yuburoll/ANSIC/images/ansicBackplates.jpg

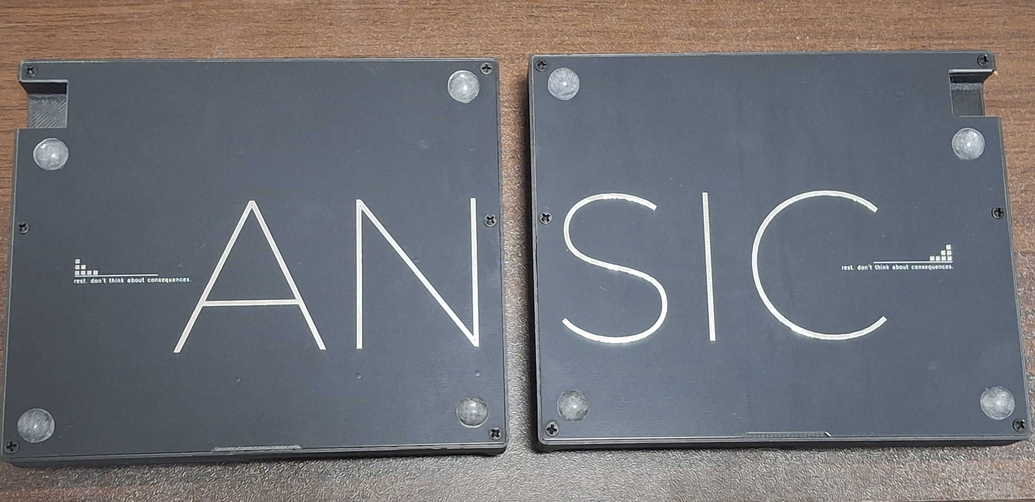
images/ansicBackplates.jpg
