yuburoll/ANSIC/images/ansicChipset1.jpg

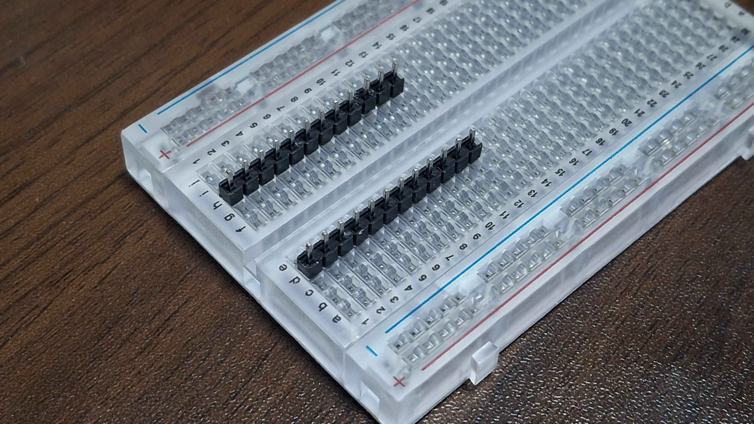
images/ansicChipset1.jpg
