yuburoll/ANSIC/images/ansicChipset2.jpg

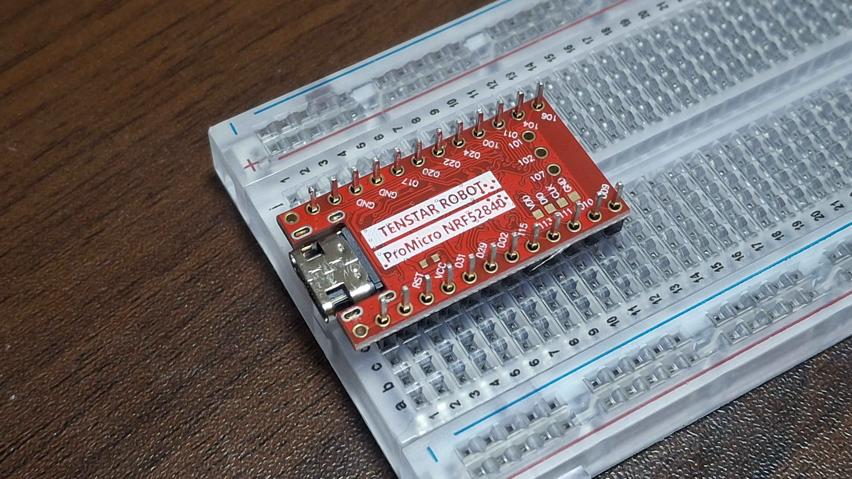
images/ansicChipset2.jpg
