yuburoll/ANSIC/images/ansicChipset3.jpg

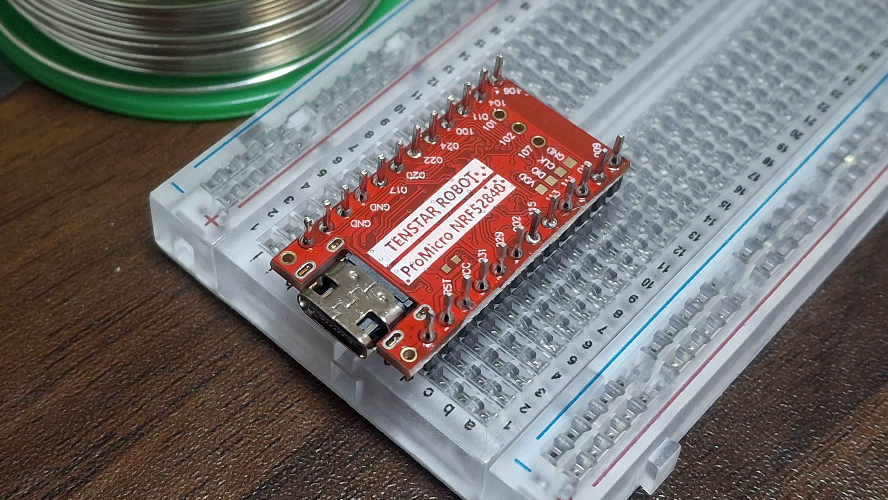
images/ansicChipset3.jpg
