yuburoll/ANSIC/images/ansicDiodes1.jpg

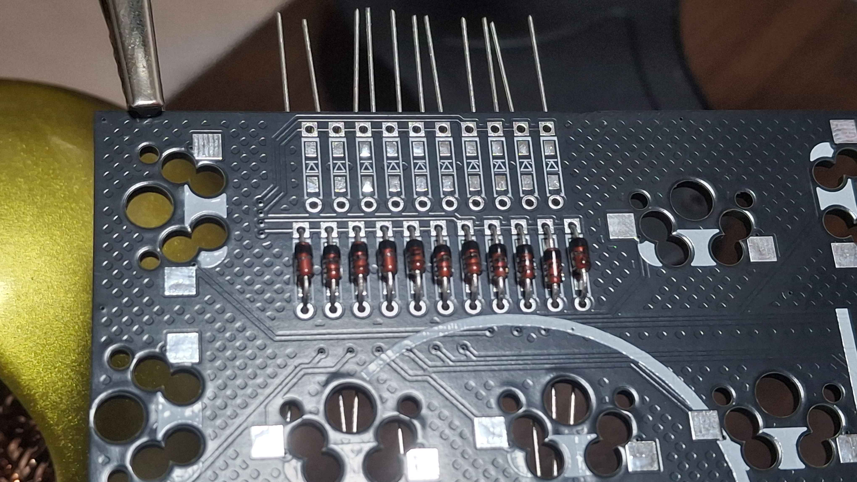
images/ansicDiodes1.jpg
