yuburoll/ANSIC/images/ansicDiodes2.jpg

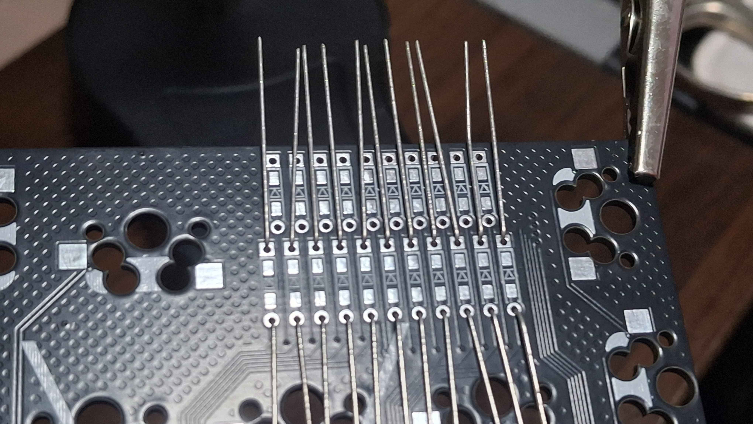
images/ansicDiodes2.jpg
