yuburoll/ANSIC/images/ansicDiodes5.jpg

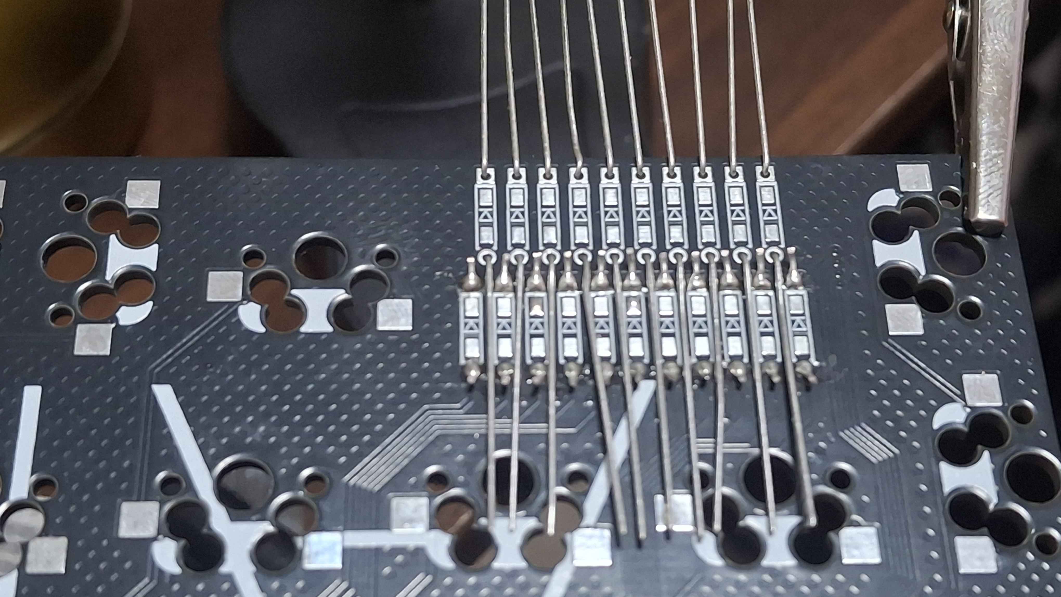
images/ansicDiodes5.jpg
