yuburoll/ANSIC/images/ansicGerber(prototype).png

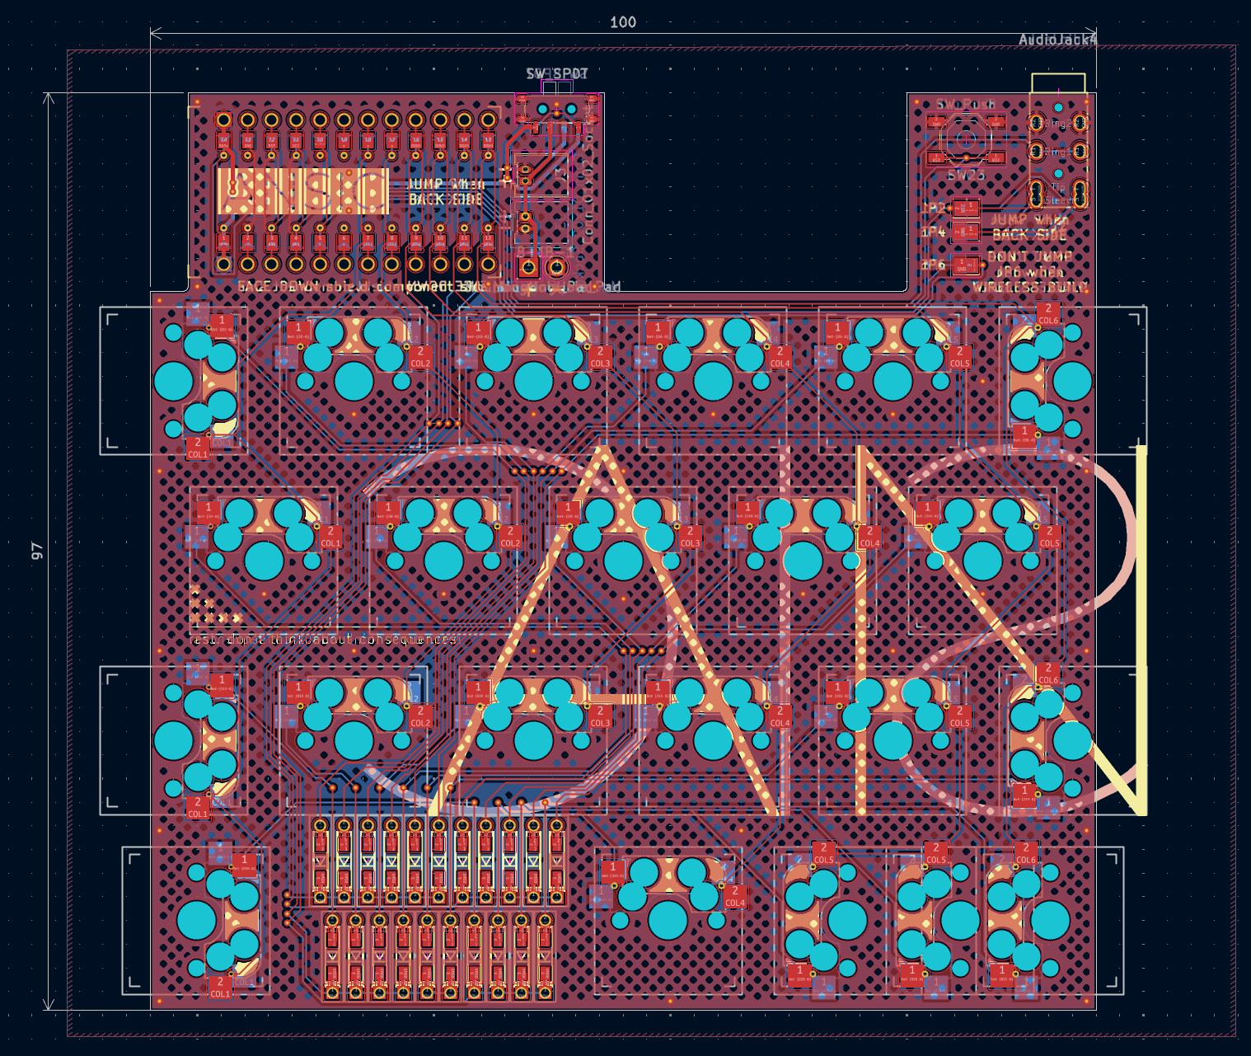
images/ansicGerber(prototype).png
