yuburoll/ANSIC/images/ansicOrientation1.jpg

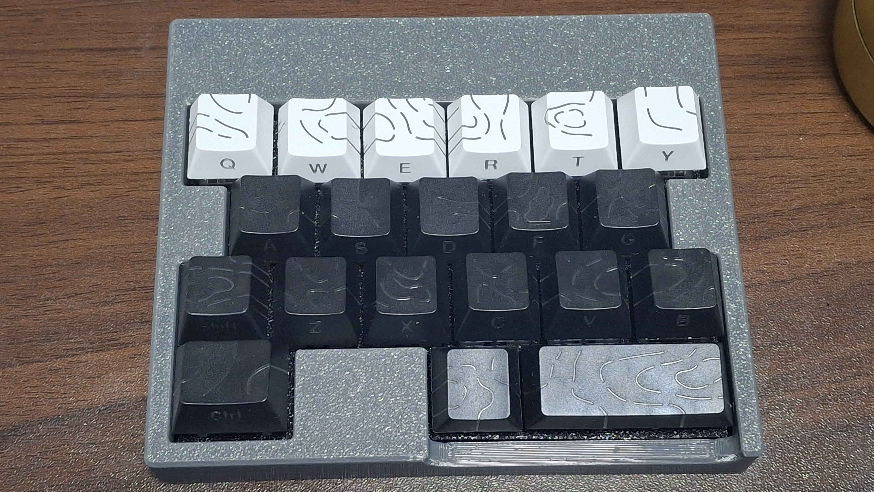
images/ansicOrientation1.jpg
