yuburoll/ANSIC/images/ansicWirelessBatteryPos1.jpg

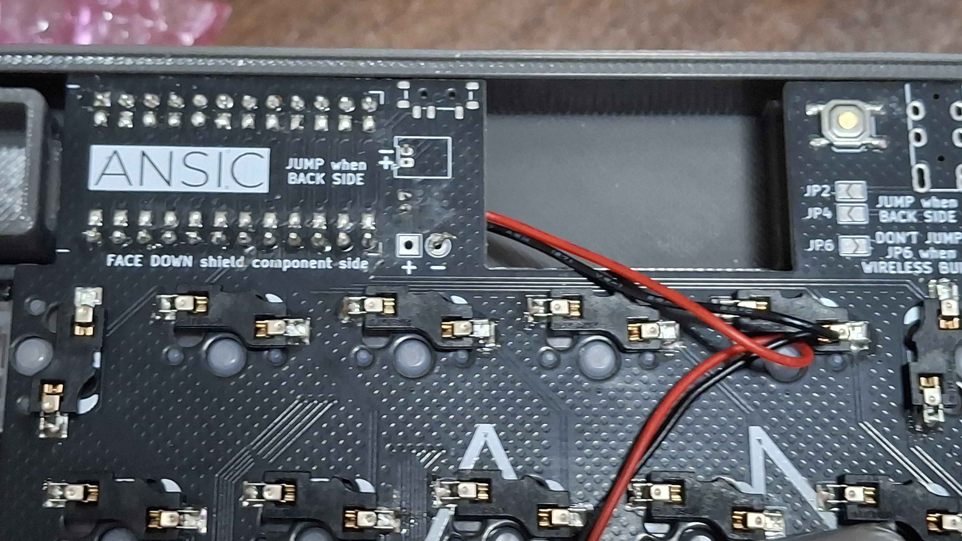
images/ansicWirelessBatteryPos1.jpg
