yuburoll/ANSIC/images/ansicWirelessBatteryPos2.jpg

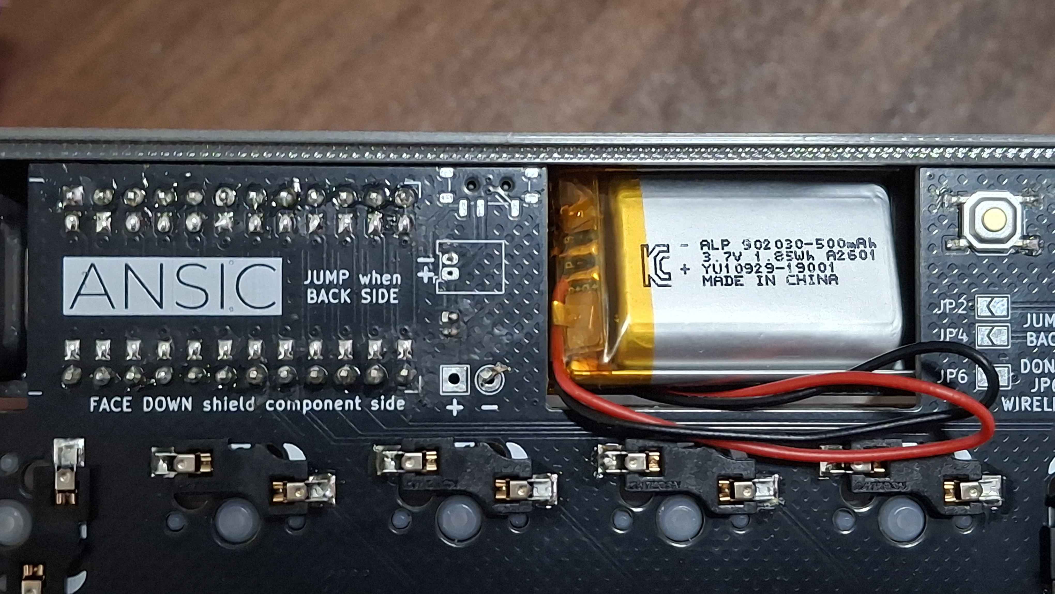
images/ansicWirelessBatteryPos2.jpg
