yuburoll/ANSIC/images/ansicWirelessBatterySwitch.jpg

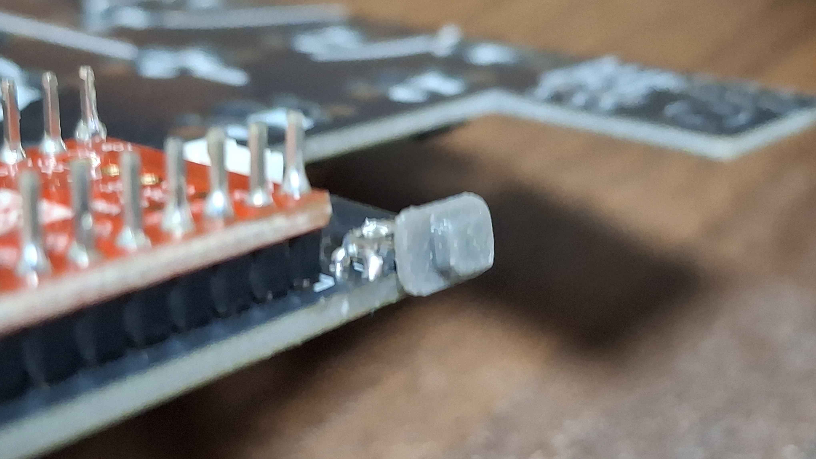
images/ansicWirelessBatterySwitch.jpg
