yuburoll/ANSIC/images/ansicWirelessSwitch2.jpg

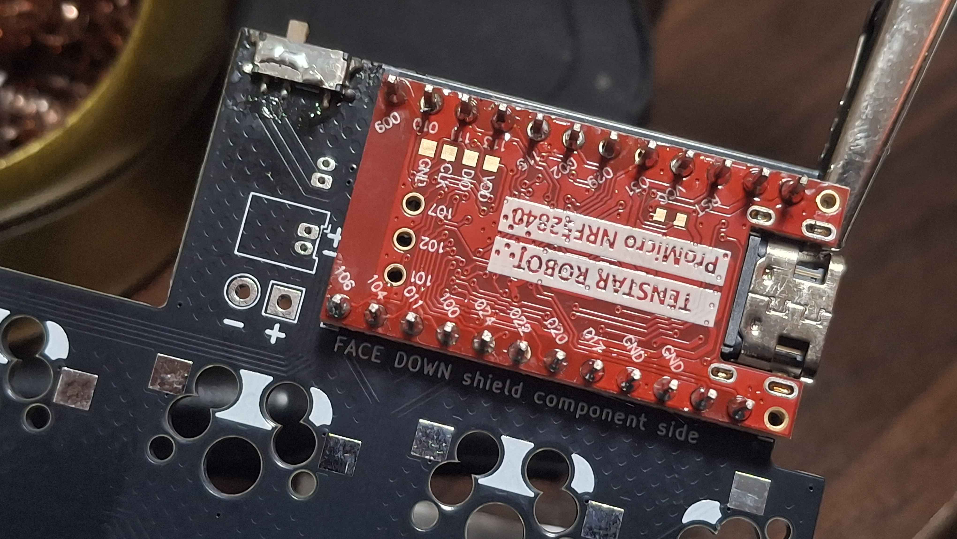
images/ansicWirelessSwitch2.jpg
