yuburoll/ANSIC/images/ansicWiredComponents1.jpg

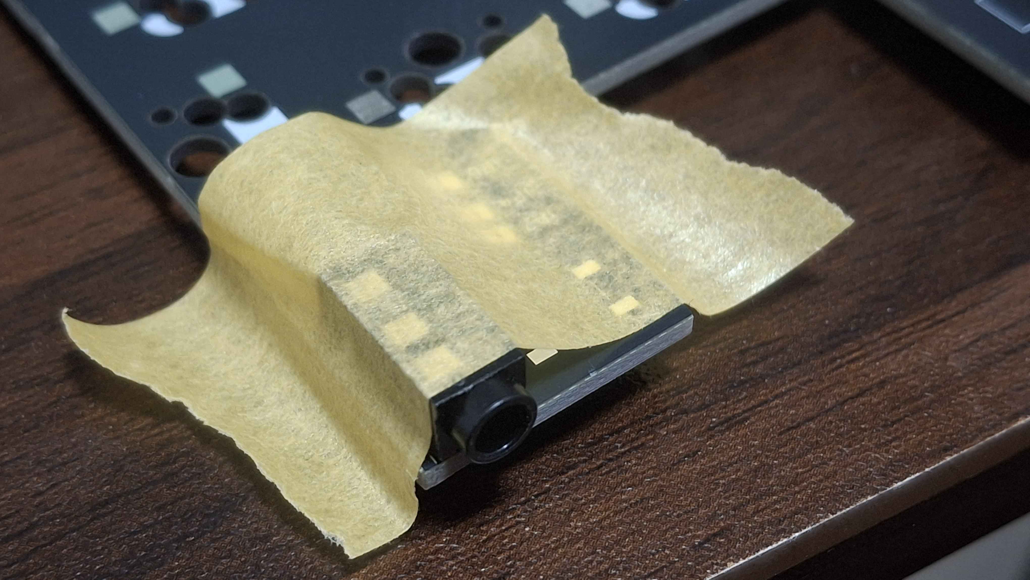
images/ansicWiredComponents1.jpg
