yuburoll/ANSIC/images/ansicWiredComponents2.jpg

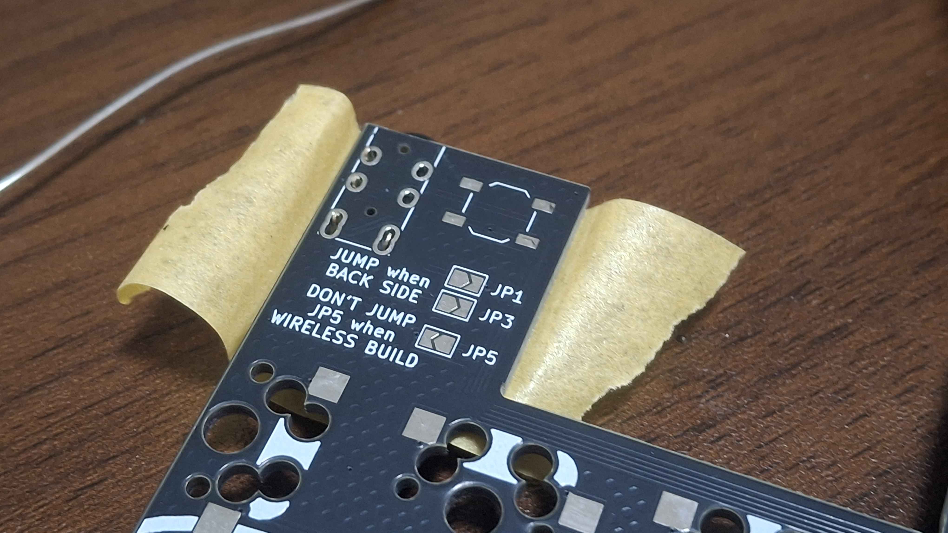
images/ansicWiredComponents2.jpg
