yuburoll/ANSIC/case/step/plates/ansicBackDefaultL.stp

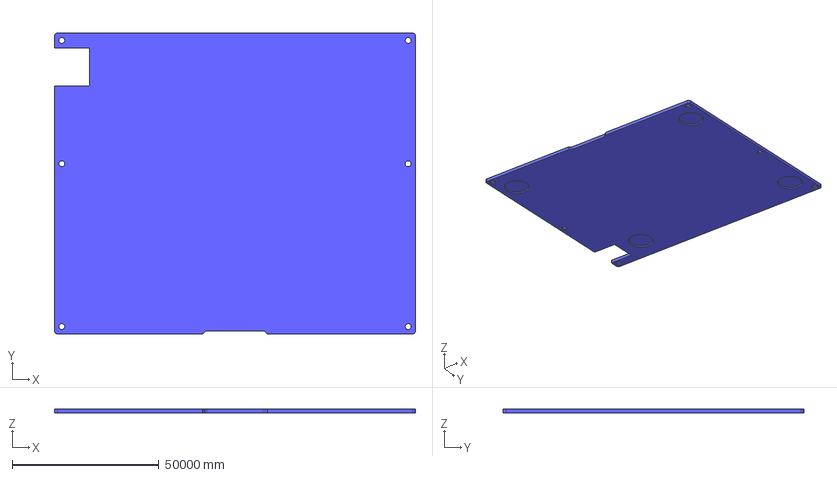
[picture p43: CAD file, 2026-01-29]
case/step/plates/ansicBackDefaultL.stp
123000.0 x 102500.0 x 1500.0 mm
